Zhang-Yong/CNC/my_CNC_Solidworks_File/┴у╝■═╝╞м/1560_GB.JPG

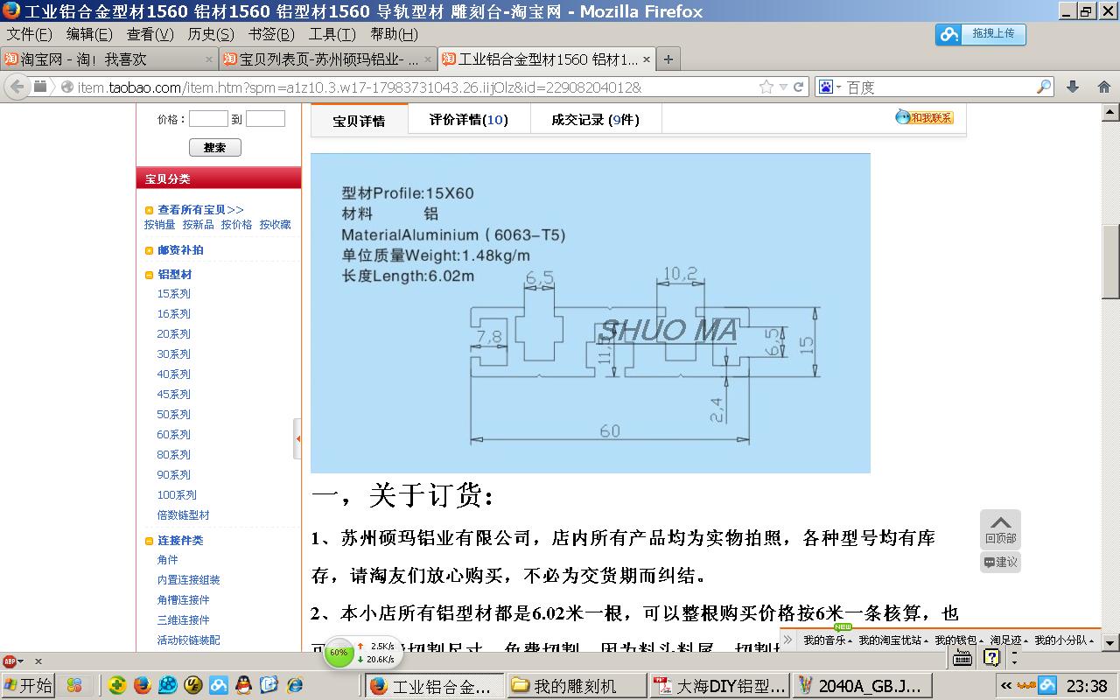
my_CNC_Solidworks_File/┴у╝■═╝╞м/1560_GB.JPG
