Zhang-Yong/CNC/my_CNC_Solidworks_File/┴у╝■═╝╞м/2040A_GB.JPG

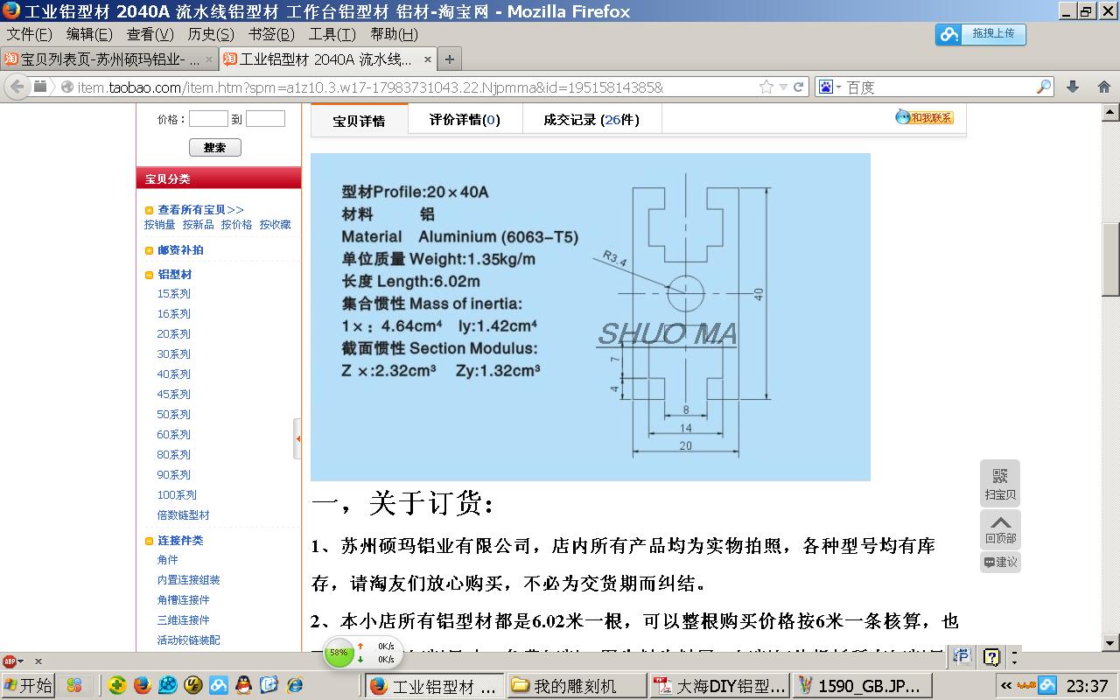
my_CNC_Solidworks_File/┴у╝■═╝╞м/2040A_GB.JPG
