Zhang-Yong/CNC/my_CNC_Solidworks_File/2040_GB_Z_75.SLDPRT

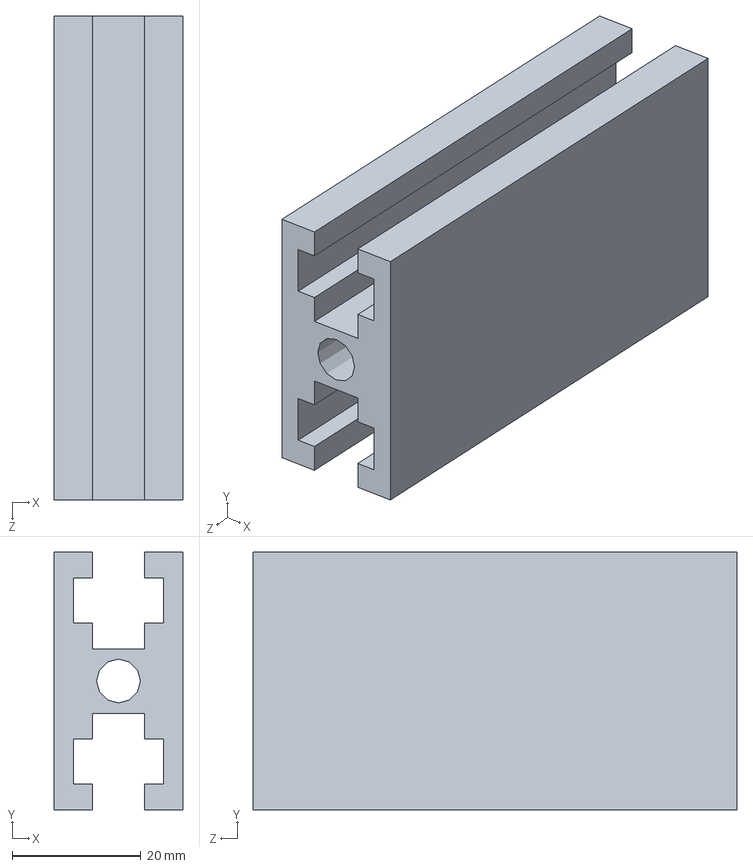
[picture p28: CAD file, 2017-07-24]
my_CNC_Solidworks_File/2040_GB_Z_75.SLDPRT
20.0 x 40.0 x 75.0 mm
