Zhang-Yong/CNC/my_CNC_Solidworks_File/SCS16LUU.SLDPRT

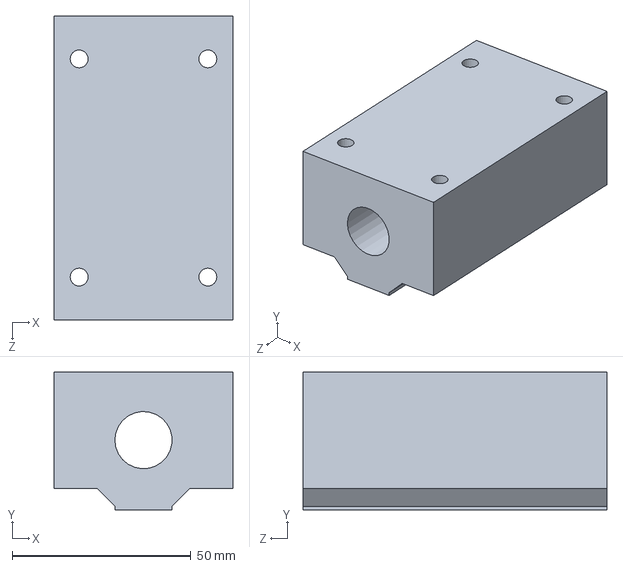
[picture p29: CAD file, 2017-07-24]
my_CNC_Solidworks_File/SCS16LUU.SLDPRT
50.0 x 38.5 x 85.0 mm
