Zhang-Yong/CNC/my_CNC_Solidworks_File/1560_110_Z_╧┬░х.SLDPRT

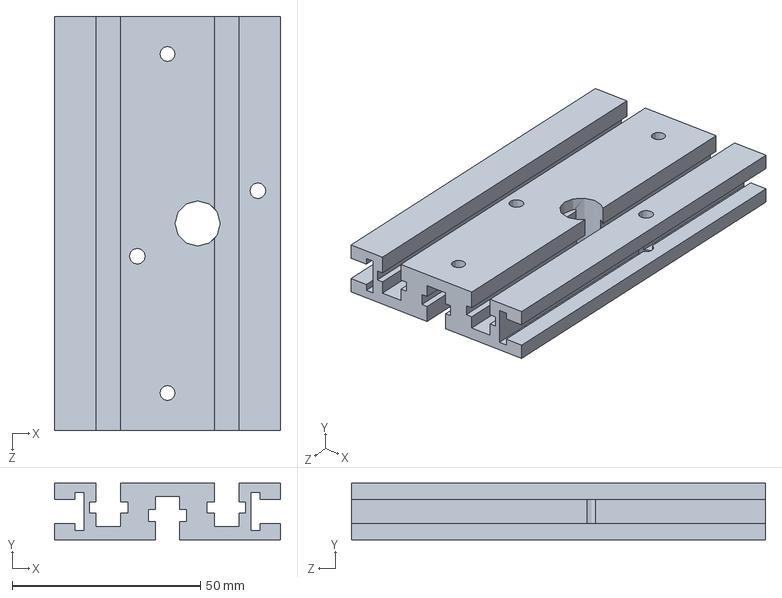
[picture p30: CAD file, 2017-07-24]
my_CNC_Solidworks_File/1560_110_Z_╧┬░х.SLDPRT
60.0 x 15.0 x 110.0 mm
