Zhang-Yong/CNC/my_CNC_Solidworks_File/SCS8LUU.SLDPRT

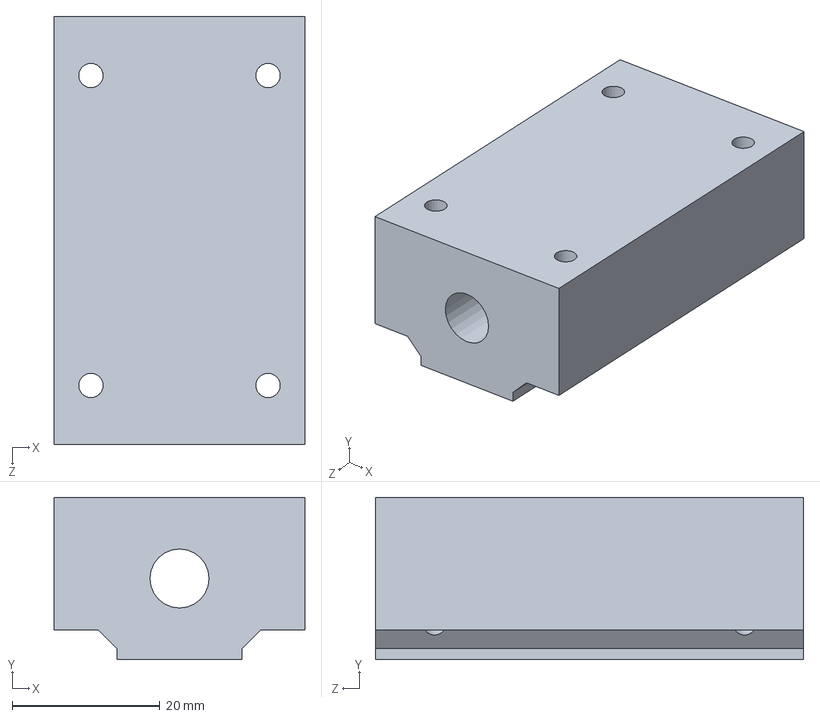
[picture p31: CAD file, 2017-07-24]
my_CNC_Solidworks_File/SCS8LUU.SLDPRT
34.0 x 22.0 x 58.0 mm
