Zhang-Yong/CNC/my_CNC_Solidworks_File/╣Ў╓щ╦┐╕╦_Y╓с_T1605.SLDPRT

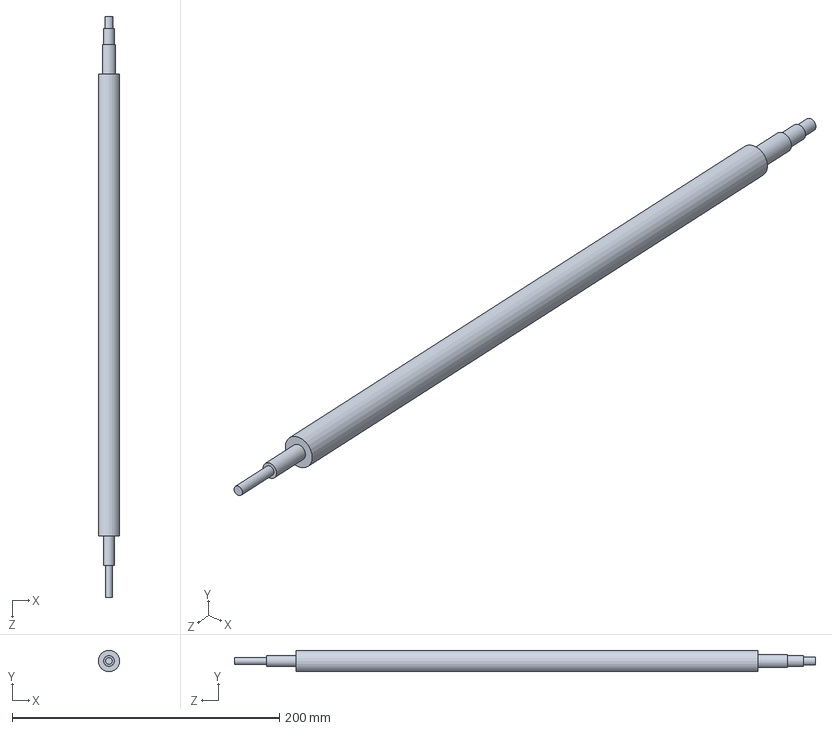
[picture p32: CAD file, 2017-07-24]
my_CNC_Solidworks_File/╣Ў╓щ╦┐╕╦_Y╓с_T1605.SLDPRT
16.0 x 16.0 x 435.0 mm
