Zhang-Yong/CNC/my_CNC_Solidworks_File/2080_160_Y_Front_╩╓┬╓.SLDPRT

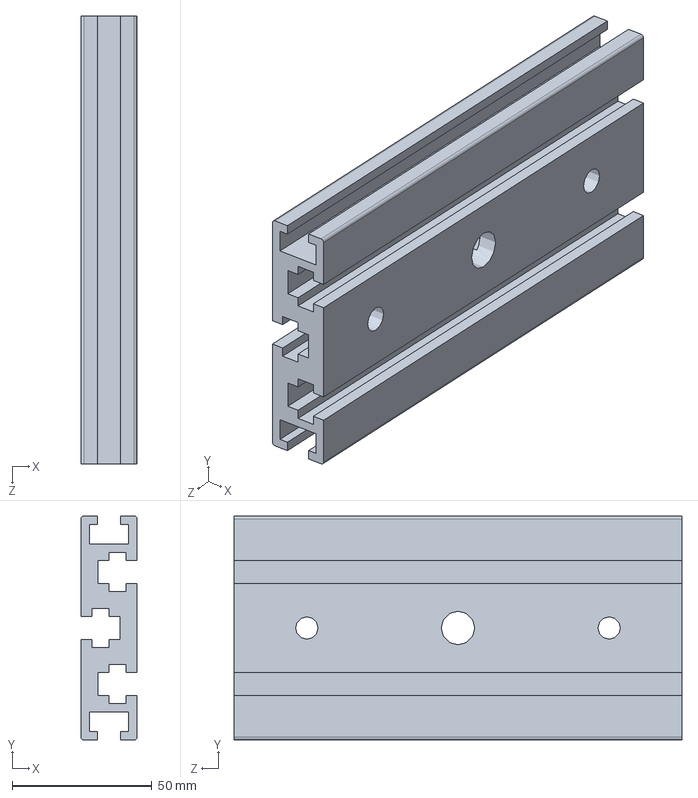
[picture p33: CAD file, 2017-07-24]
my_CNC_Solidworks_File/2080_160_Y_Front_╩╓┬╓.SLDPRT
20.0 x 80.0 x 160.0 mm
