Zhang-Yong/CNC/my_CNC_Solidworks_File/2040_GB_XY_60.SLDPRT

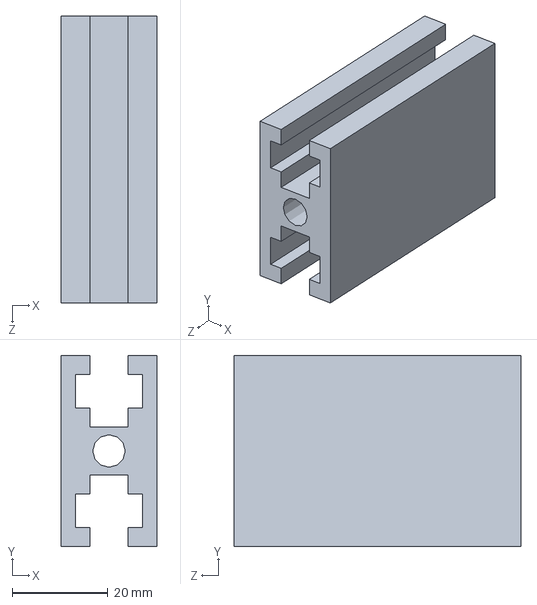
[picture p34: CAD file, 2017-07-24]
my_CNC_Solidworks_File/2040_GB_XY_60.SLDPRT
20.0 x 40.0 x 60.0 mm
