Zhang-Yong/CNC/my_CNC_Solidworks_File/1590_200_X.SLDPRT

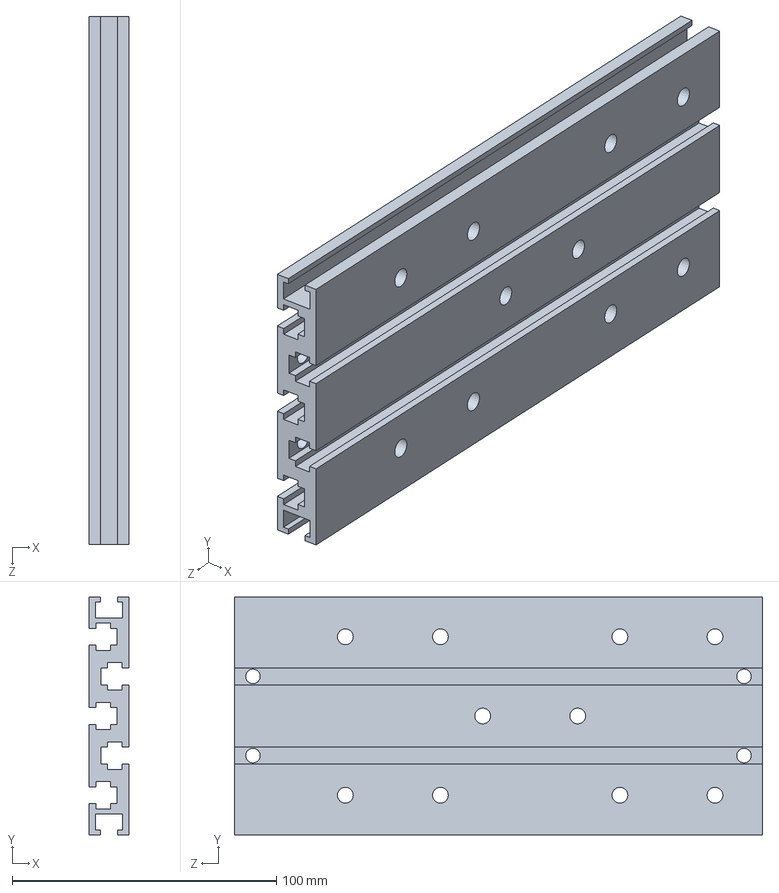
[picture p35: CAD file, 2017-07-24]
my_CNC_Solidworks_File/1590_200_X.SLDPRT
15.0 x 90.0 x 200.0 mm
