Zhang-Yong/CNC/my_CNC_Solidworks_File/╣Ў╓щ╦┐╕╦_Y╓с_T1605_new.SLDPRT

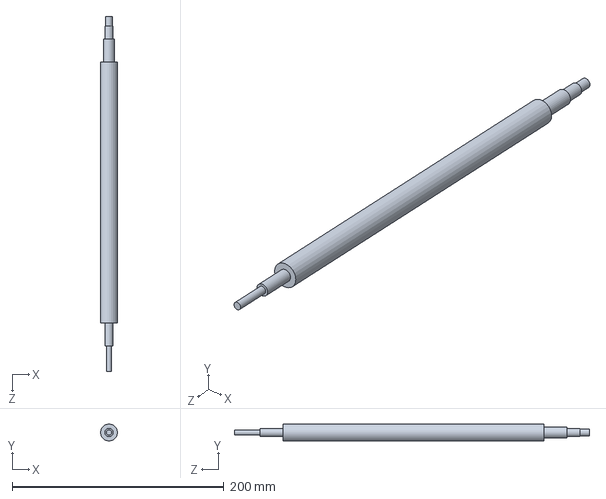
[picture p36: CAD file, 2017-07-24]
my_CNC_Solidworks_File/╣Ў╓щ╦┐╕╦_Y╓с_T1605_new.SLDPRT
16.0 x 16.0 x 335.0 mm
