Zhang-Yong/CNC/my_CNC_Solidworks_File/1590_290_Y.SLDPRT

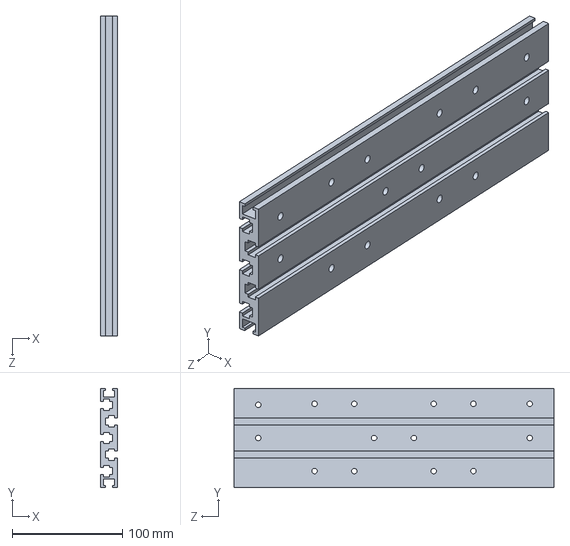
[picture p37: CAD file, 2017-07-24]
my_CNC_Solidworks_File/1590_290_Y.SLDPRT
15.0 x 90.0 x 290.0 mm
