Zhang-Yong/CNC/my_CNC_Solidworks_File/SCS16UU.SLDPRT

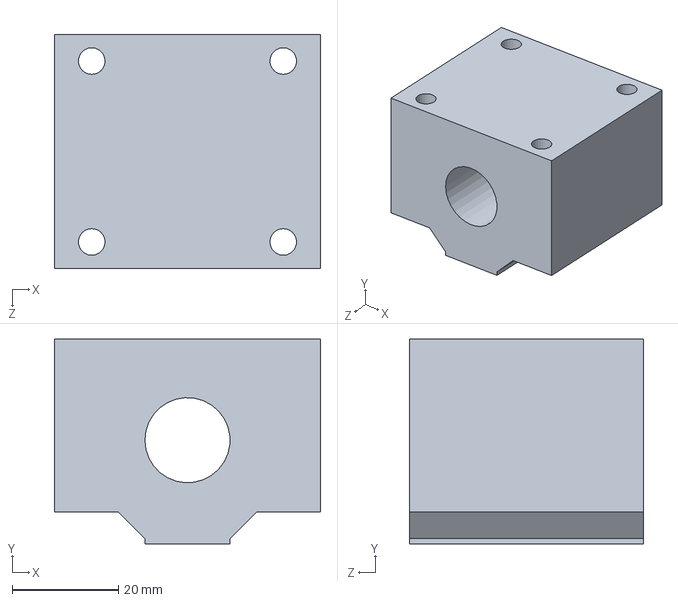
[picture p38: CAD file, 2017-07-24]
my_CNC_Solidworks_File/SCS16UU.SLDPRT
50.0 x 38.5 x 44.0 mm
