Zhang-Yong/CNC/my_CNC_Solidworks_File/╣т╓с16x350mm_Y╓с.SLDPRT

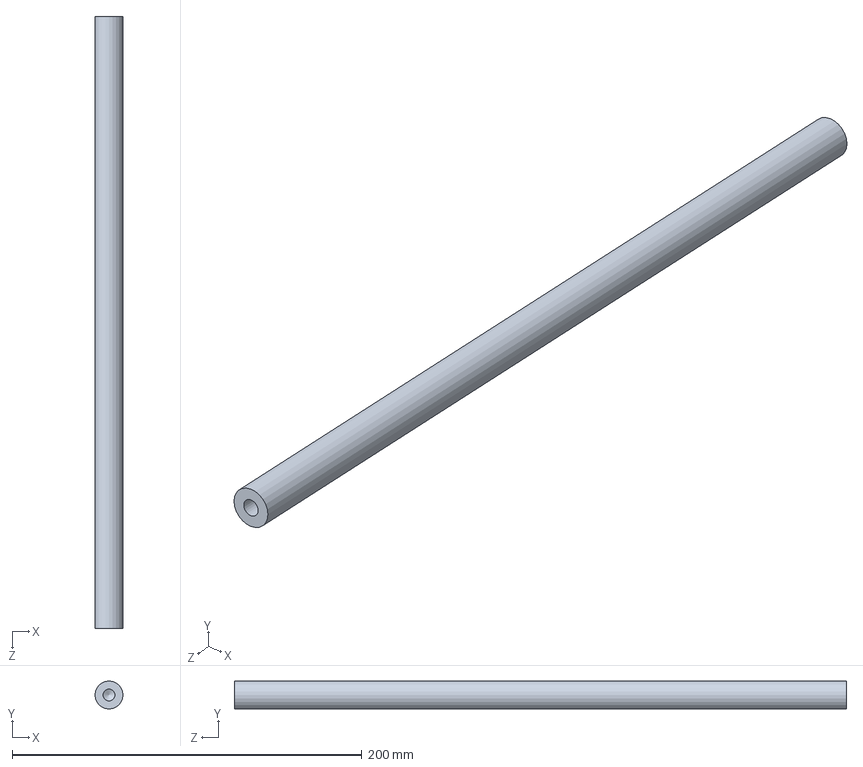
[picture p39: CAD file, 2017-07-24]
my_CNC_Solidworks_File/╣т╓с16x350mm_Y╓с.SLDPRT
16.0 x 16.0 x 350.0 mm
