Zhang-Yong/CNC/my_CNC_Solidworks_File/KFL08_╓с╫∙.SLDPRT

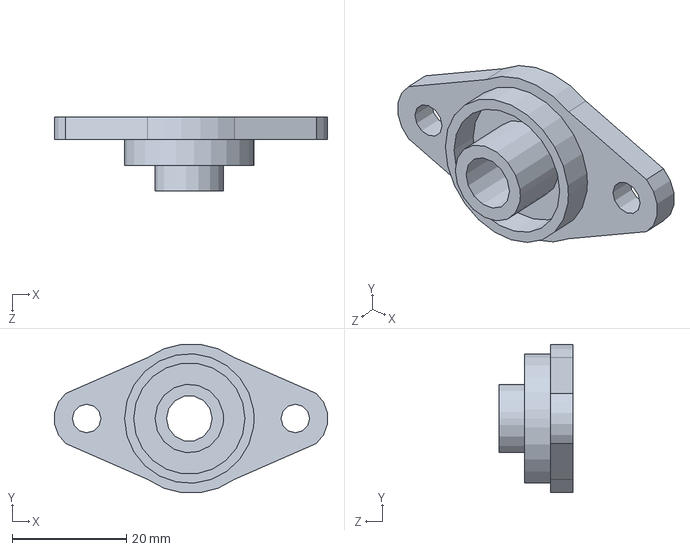
[picture p40: CAD file, 2017-07-24]
my_CNC_Solidworks_File/KFL08_╓с╫∙.SLDPRT
47.7 x 26.0 x 13.0 mm
