Zhang-Yong/CNC/my_CNC_Solidworks_File/╣т╓с16x260mm_X╓с.SLDPRT

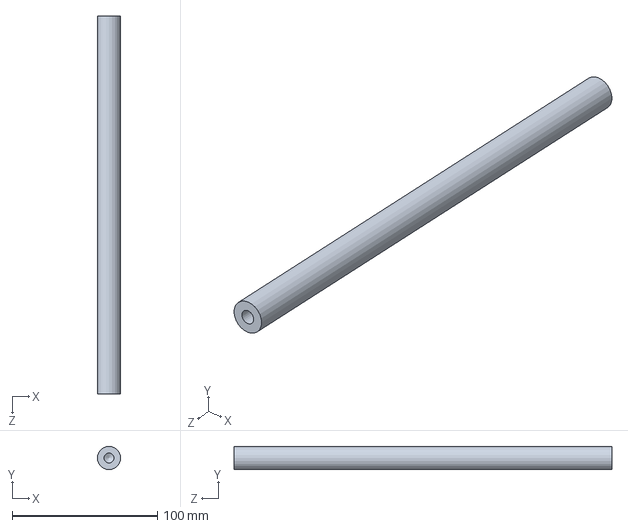
[picture p41: CAD file, 2017-07-24]
my_CNC_Solidworks_File/╣т╓с16x260mm_X╓с.SLDPRT
16.0 x 16.0 x 260.0 mm
