Zhang-Yong/CNC/my_CNC_Solidworks_File/╣Ў╓щ╦┐╕╦1605┬▌─╕.SLDPRT

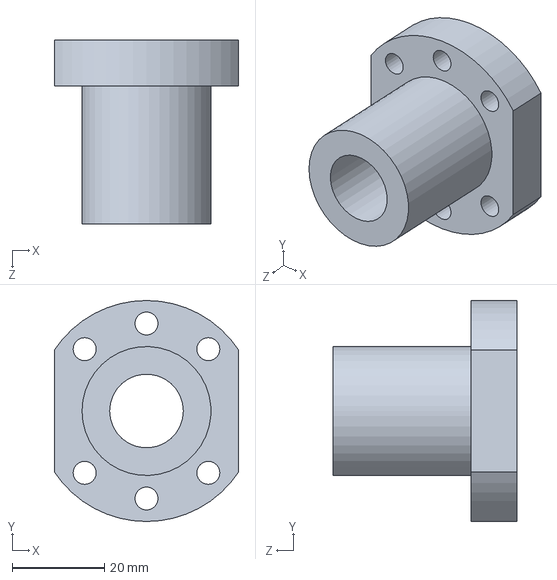
[picture p42: CAD file, 2017-07-24]
my_CNC_Solidworks_File/╣Ў╓щ╦┐╕╦1605┬▌─╕.SLDPRT
40.0 x 48.0 x 40.0 mm
