Zhang-Yong/CNC/my_CNC_Solidworks_File/╣т╓с8x170mm_Z╓с.SLDPRT

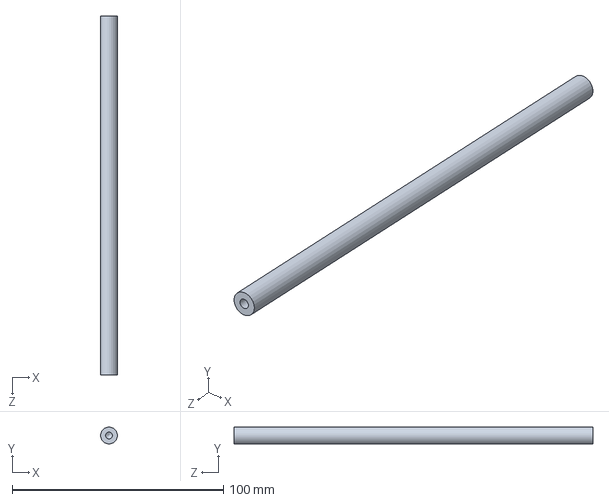
[picture p43: CAD file, 2017-07-24]
my_CNC_Solidworks_File/╣т╓с8x170mm_Z╓с.SLDPRT
8.00 x 8.00 x 170.0 mm
