Zhang-Yong/CNC/my_CNC_Solidworks_File/╣Ў╓щ╦┐╕╦_Z╓с_T1605.SLDPRT

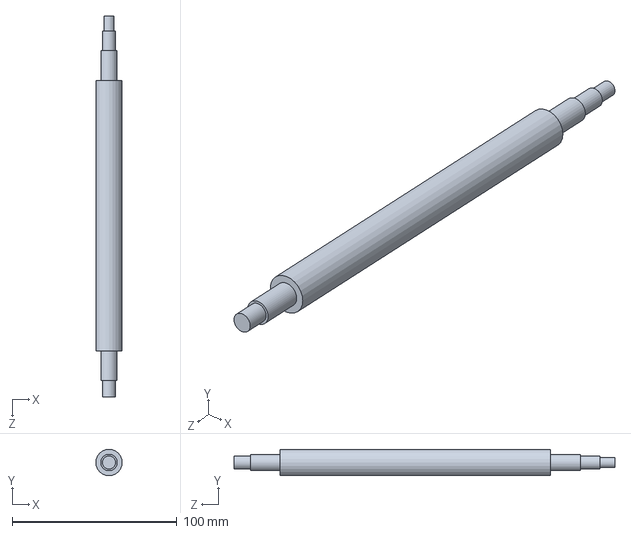
[picture p44: CAD file, 2017-07-24]
my_CNC_Solidworks_File/╣Ў╓щ╦┐╕╦_Z╓с_T1605.SLDPRT
16.0 x 16.0 x 231.0 mm
