Zhang-Yong/CNC/my_CNC_Solidworks_File/╓ў╓с╡ч╗·.SLDPRT

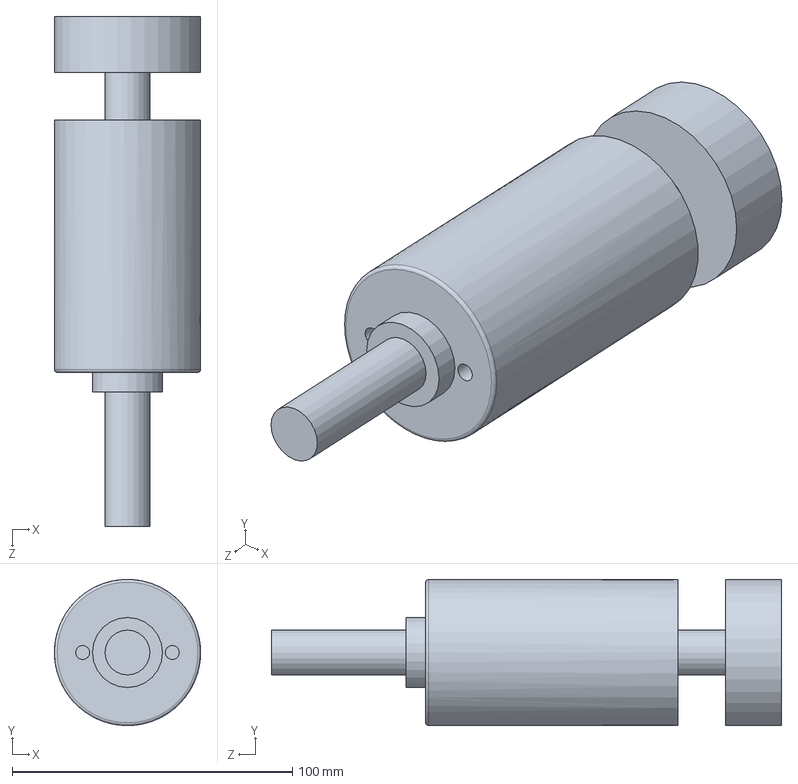
[picture p45: CAD file, 2017-07-24]
my_CNC_Solidworks_File/╓ў╓с╡ч╗·.SLDPRT
52.2 x 52.1 x 182.0 mm
