Zhang-Yong/CNC/my_CNC_Solidworks_File/╣т╓с16x250mm_Y╓с_new.SLDPRT

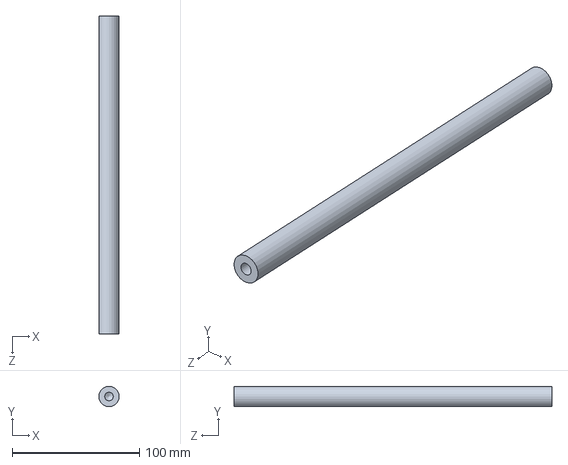
[picture p46: CAD file, 2017-07-24]
my_CNC_Solidworks_File/╣т╓с16x250mm_Y╓с_new.SLDPRT
16.0 x 16.0 x 250.0 mm
