Zhang-Yong/CNC/my_CNC_Solidworks_File/SCS16UU_Half.SLDPRT

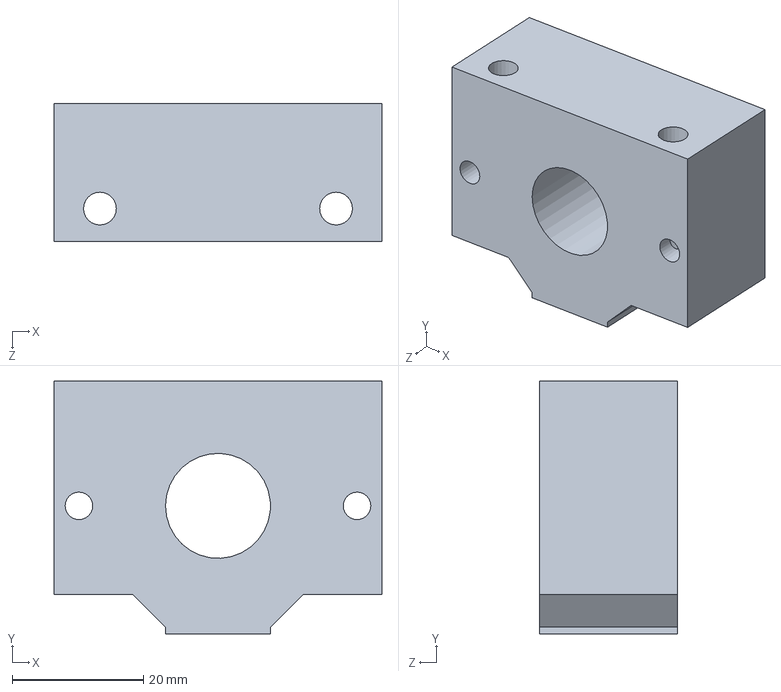
[picture p47: CAD file, 2017-07-24]
my_CNC_Solidworks_File/SCS16UU_Half.SLDPRT
50.0 x 38.5 x 21.0 mm
