Zhang-Yong/CNC/my_CNC_Solidworks_File/2080_128_Z.SLDPRT

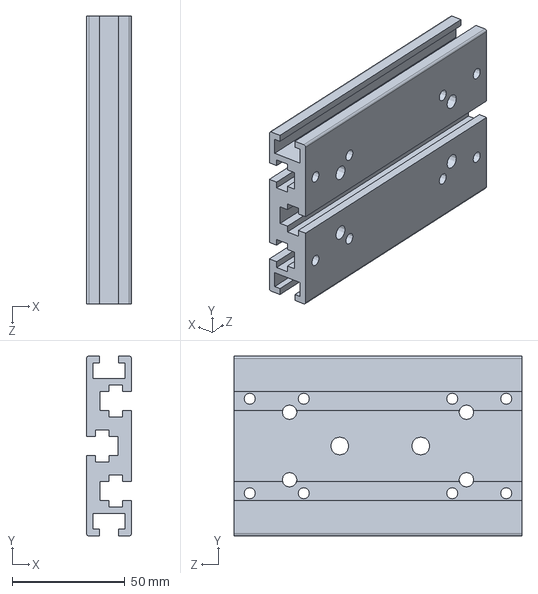
[picture p49: CAD file, 2017-07-24]
my_CNC_Solidworks_File/2080_128_Z.SLDPRT
20.0 x 80.0 x 128.0 mm
