Zhang-Yong/CNC/my_CNC_Solidworks_File/57▓╜╜°╡ч╗·╓с.SLDPRT

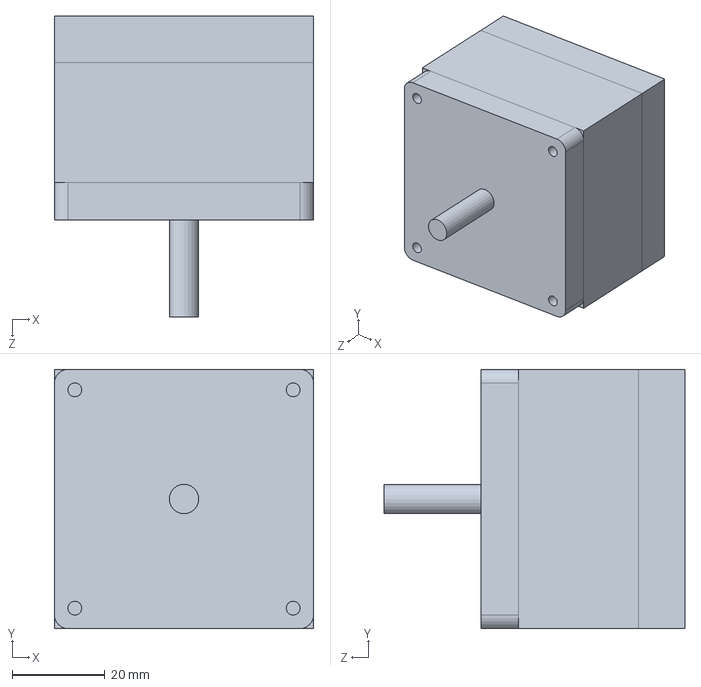
[picture p50: CAD file, 2017-05-19]
my_CNC_Solidworks_File/57▓╜╜°╡ч╗·╓с.SLDPRT
56.0 x 56.0 x 65.0 mm
