Zhang-Yong/CNC/my_CNC_Solidworks_File/1530_50_XY .SLDPRT

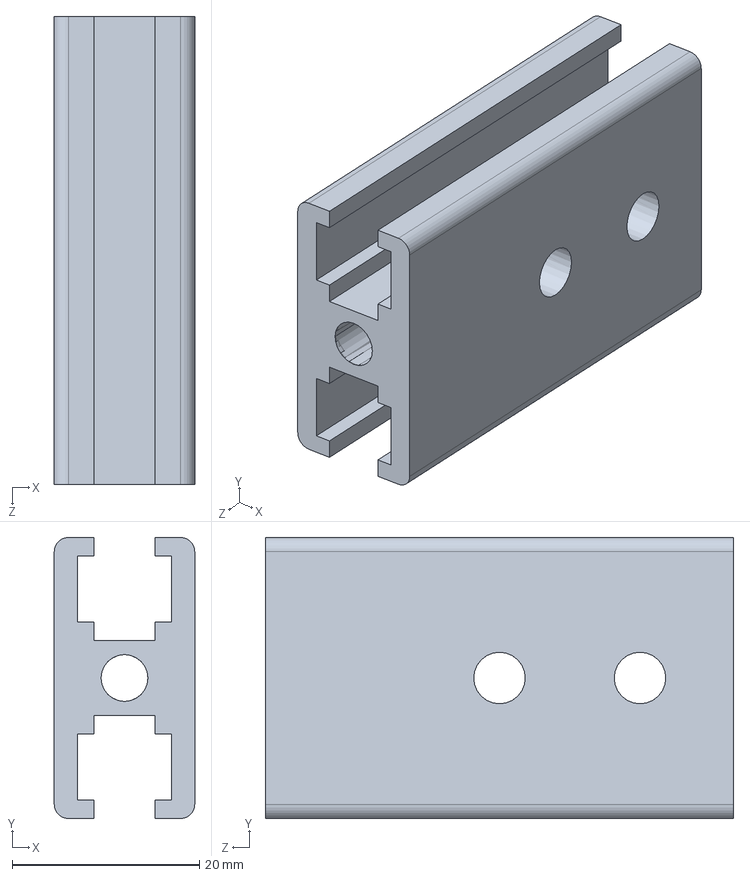
[picture p51: CAD file, 2017-05-19]
my_CNC_Solidworks_File/1530_50_XY .SLDPRT
15.0 x 30.0 x 50.0 mm
