Zhang-Yong/CNC/my_CNC_Solidworks_File/1530_260_X .SLDPRT

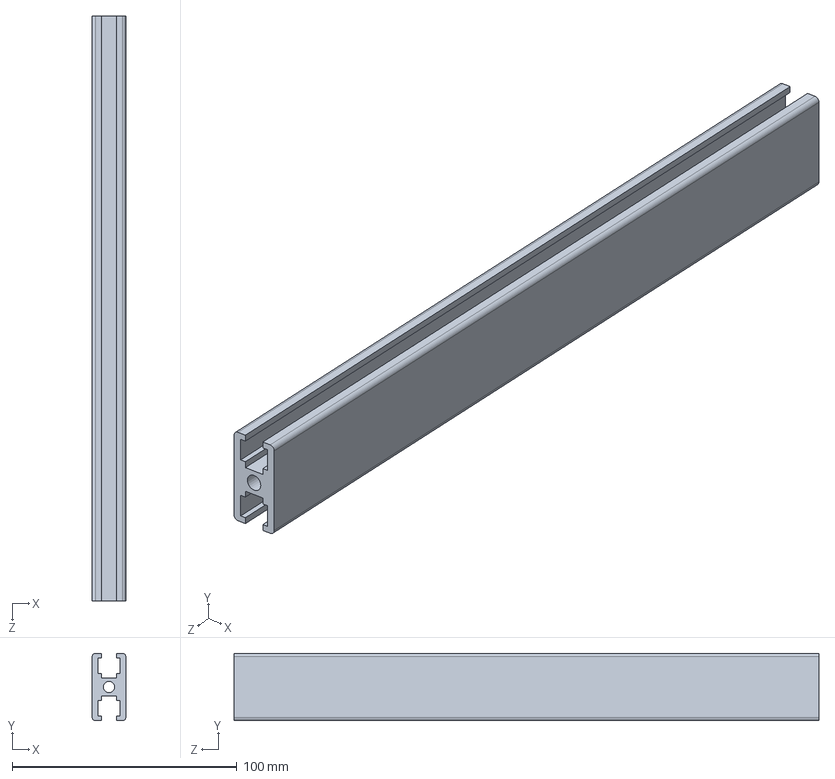
[picture p52: CAD file, 2017-05-19]
my_CNC_Solidworks_File/1530_260_X .SLDPRT
15.0 x 30.0 x 260.0 mm
